DimitraMTsakiridou/THESIS-UltraLowPower-LoRa-Node/Images/rx-tx.png

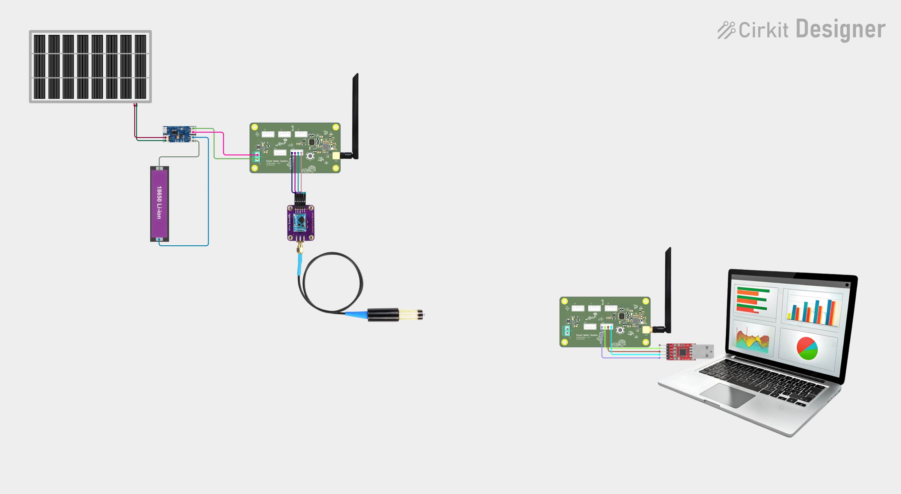
Images/rx-tx.png
