DimitraMTsakiridou/THESIS-UltraLowPower-LoRa-Node/Images/star.png

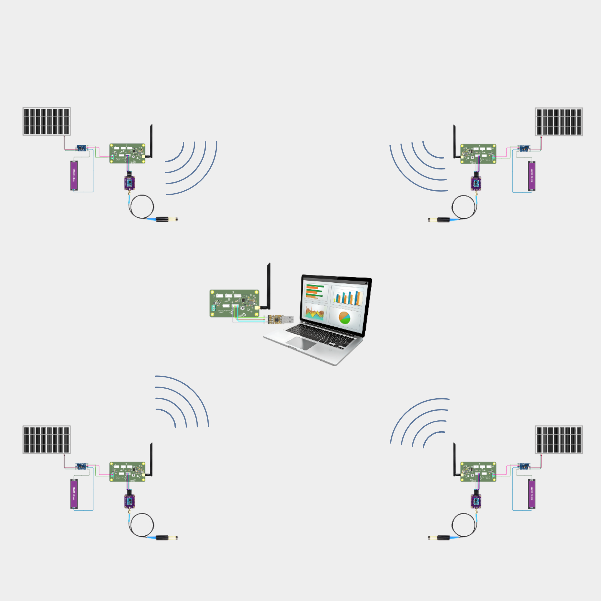
Images/star.png
