DimitraMTsakiridou/THESIS-UltraLowPower-LoRa-Node/Images/system_box.jpg

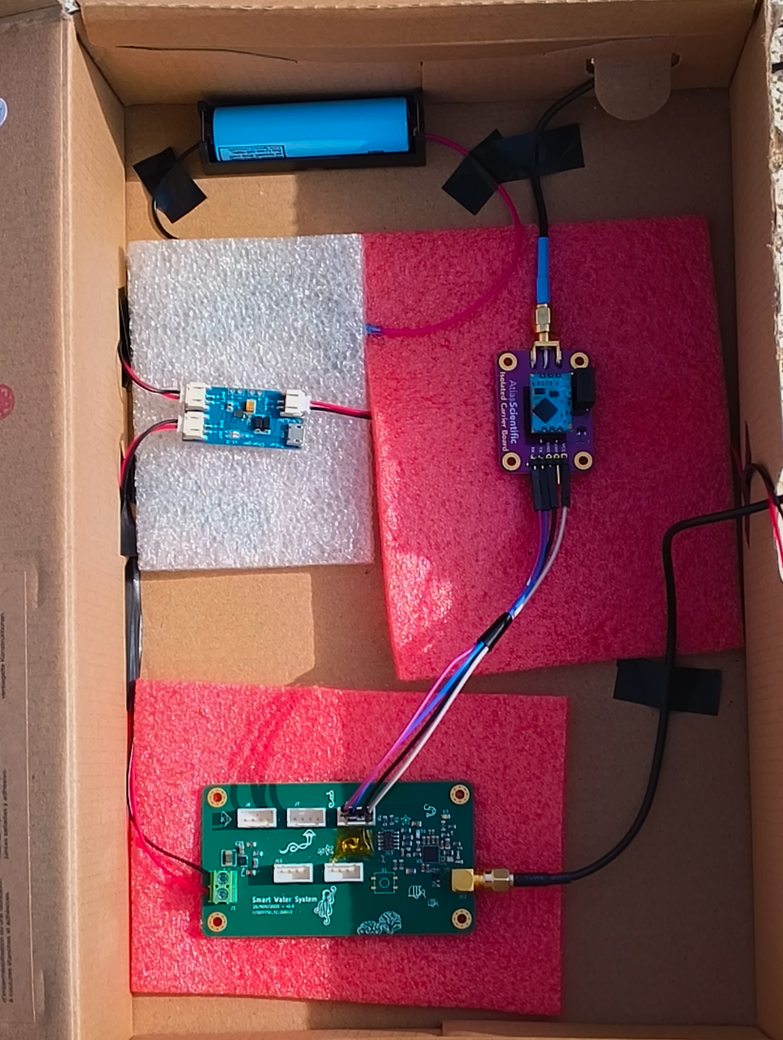
Images/system_box.jpg
