DimitraMTsakiridou/THESIS-UltraLowPower-LoRa-Node/Software/Tests/collision_test/stress_test_results.png

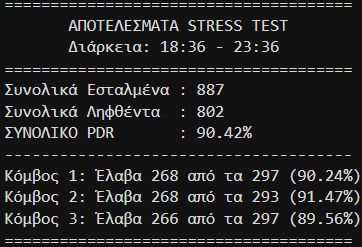
Software/Tests/collision_test/stress_test_results.png
