DimitraMTsakiridou/THESIS-UltraLowPower-LoRa-Node/Software/Tests/collision_test/Stress_Test_Results/1_PDR_BarChart.png

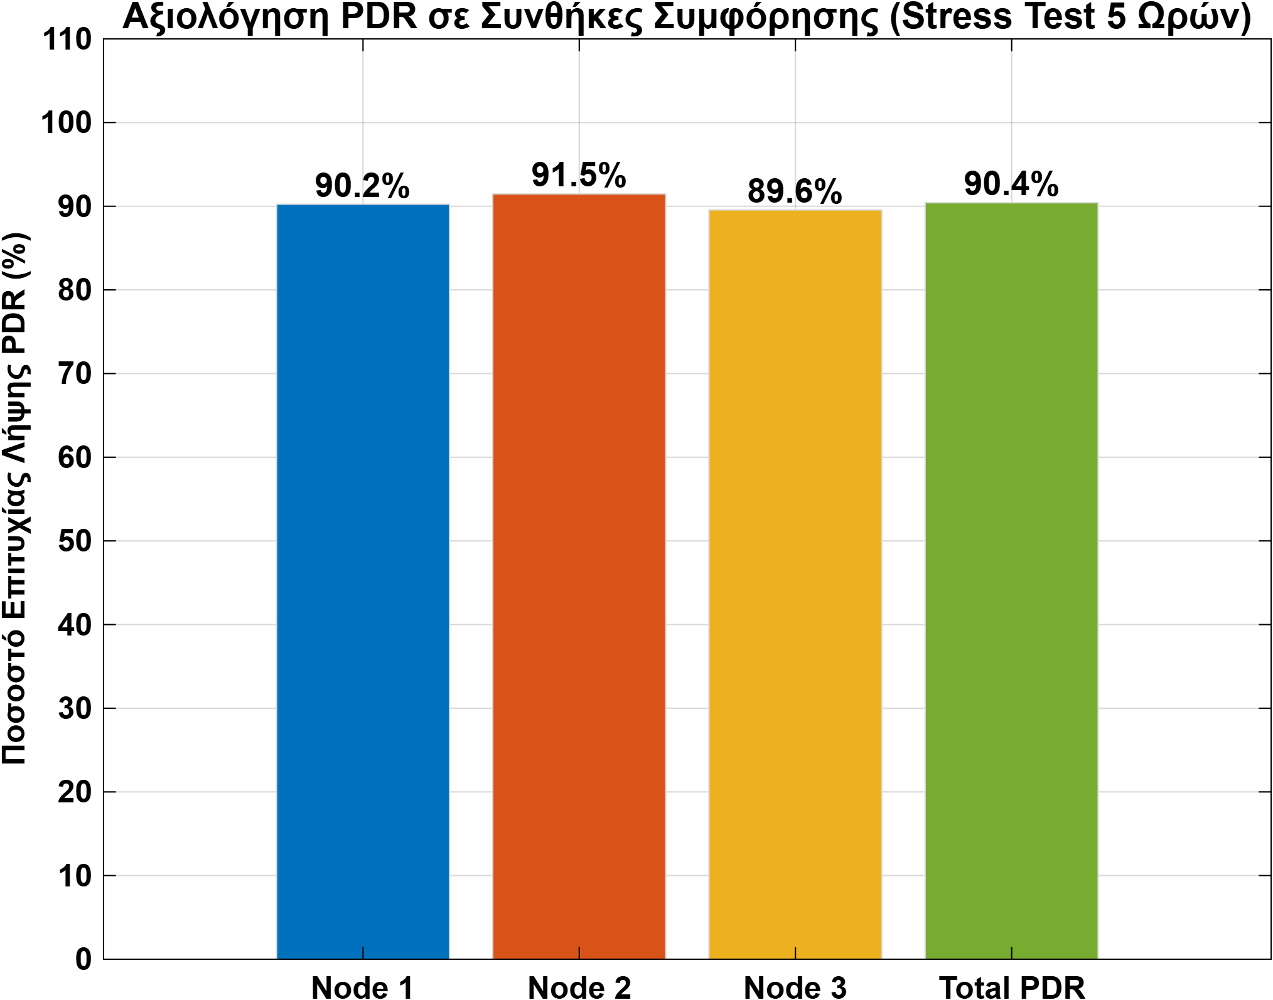
Software/Tests/collision_test/Stress_Test_Results/1_PDR_BarChart.png
