DimitraMTsakiridou/THESIS-UltraLowPower-LoRa-Node/Software/Tests/collision_test/Stress_Test_Results/2_Signal_Quality_Smoothed.png

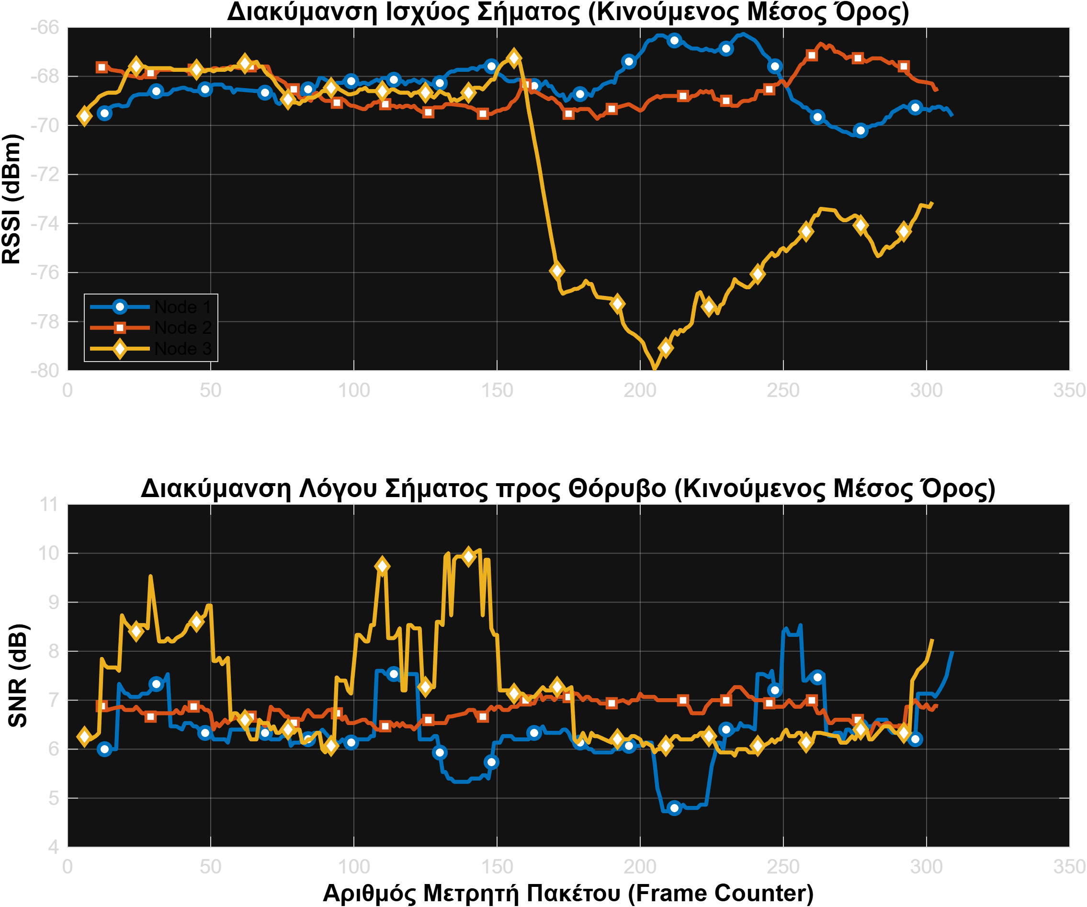
Software/Tests/collision_test/Stress_Test_Results/2_Signal_Quality_Smoothed.png
