DimitraMTsakiridou/THESIS-UltraLowPower-LoRa-Node/Software/Tests/usrp tests/1/third14.jpg

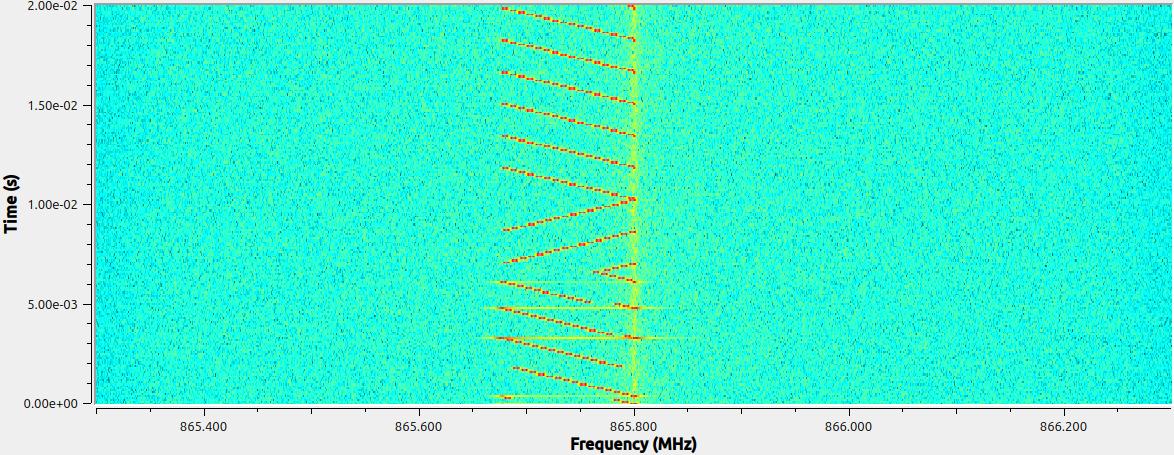
Software/Tests/usrp tests/1/third14.jpg
