DimitraMTsakiridou/THESIS-UltraLowPower-LoRa-Node/Software/Tests/usrp tests/attack.jpg

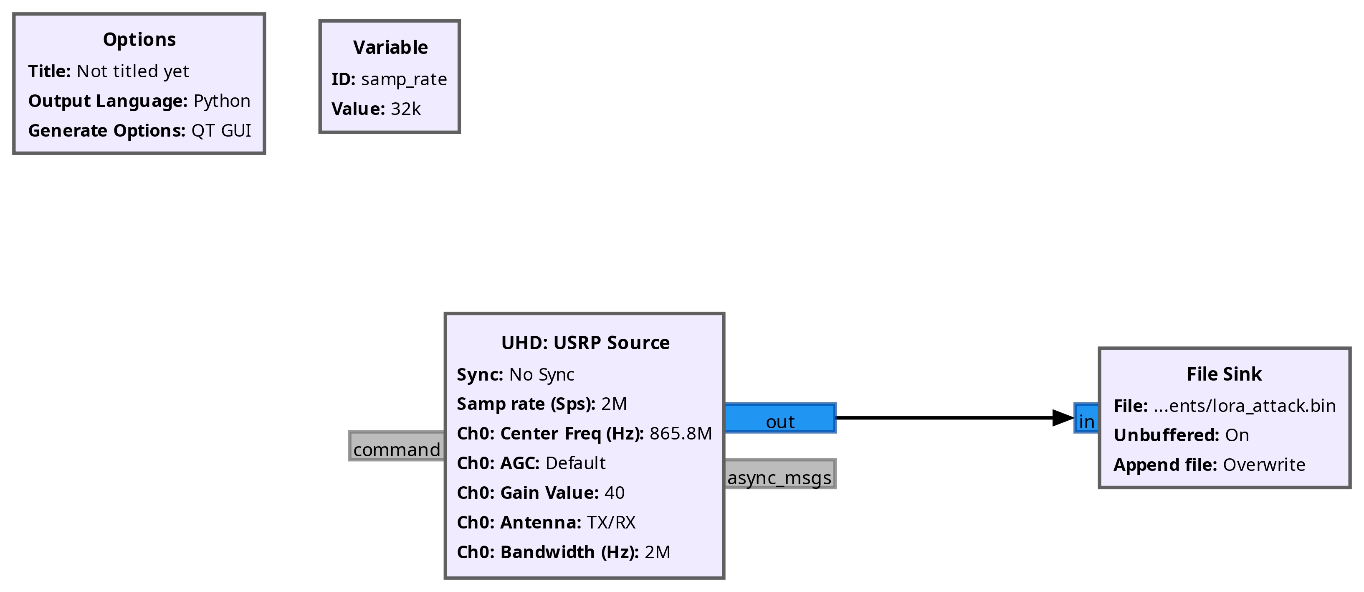
Software/Tests/usrp tests/attack.jpg
