DimitraMTsakiridou/THESIS-UltraLowPower-LoRa-Node/Software/Tests/usrp tests/rεplay.jpg

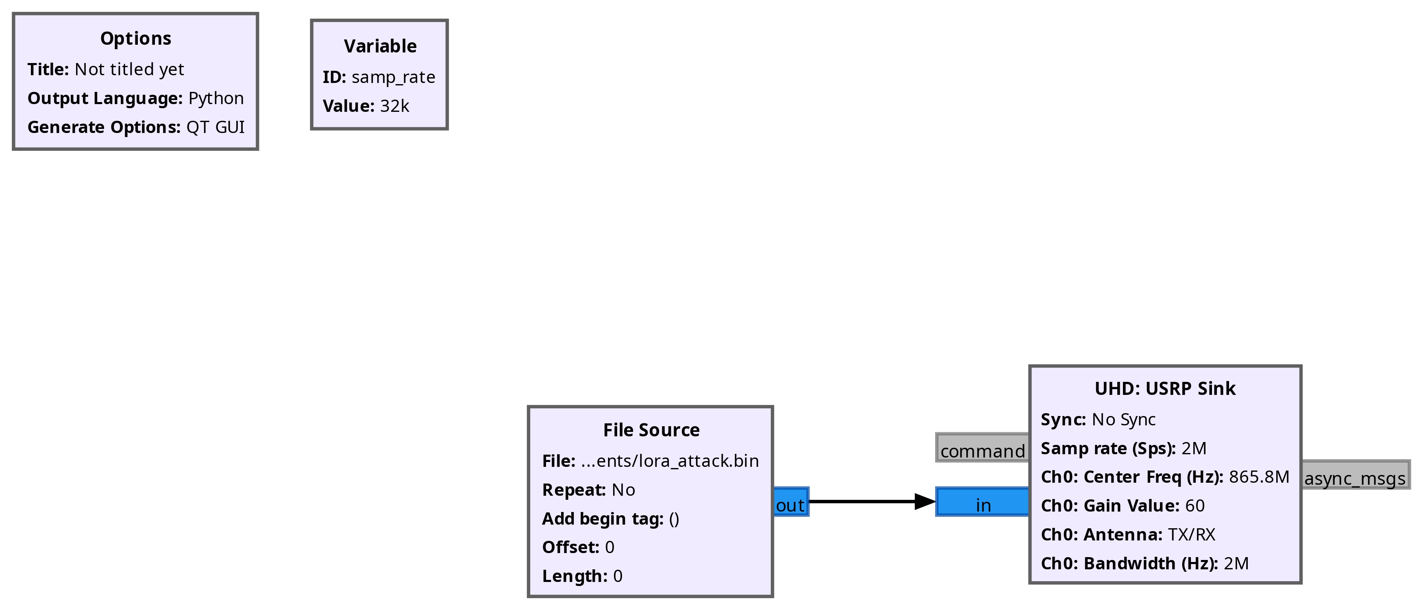
Software/Tests/usrp tests/rεplay.jpg
