DimitraMTsakiridou/THESIS-UltraLowPower-LoRa-Node/Software/Tests/usrp tests/sf8.jpg.jpg

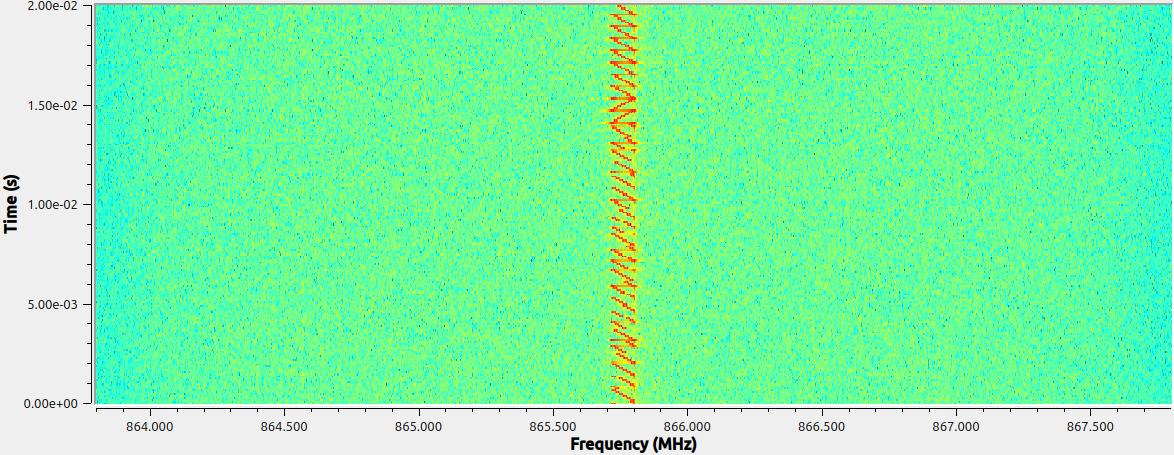
Software/Tests/usrp tests/sf8.jpg.jpg
