DimitraMTsakiridou/THESIS-UltraLowPower-LoRa-Node/Software/Tests/usrp tests/weird 22.jpg

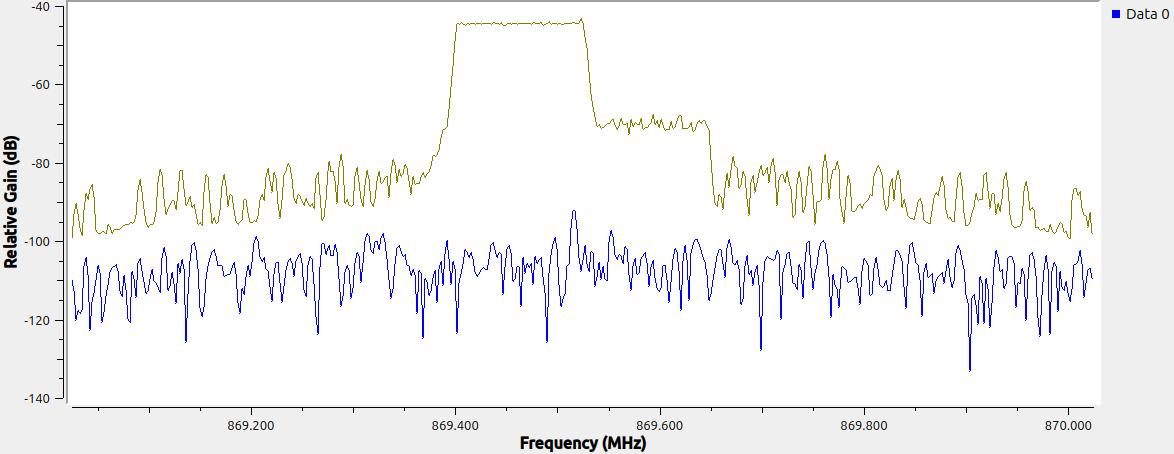
Software/Tests/usrp tests/weird 22.jpg
